ImoogDi/LesScope/doc/pictures/Backplane_bot_parts_mounted.png

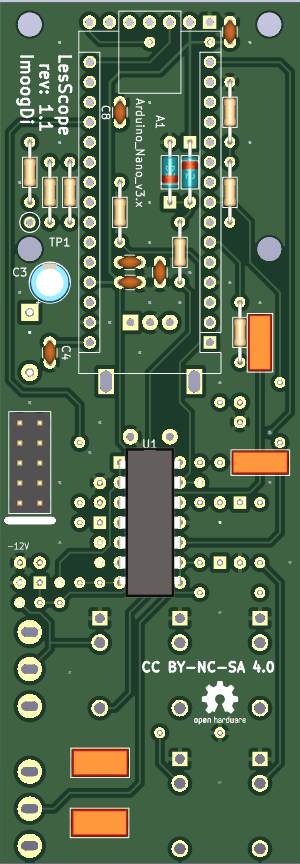
doc/pictures/Backplane_bot_parts_mounted.png
