ImoogDi/LesScope/doc/pictures/Backplane_top_parts_mounted.png

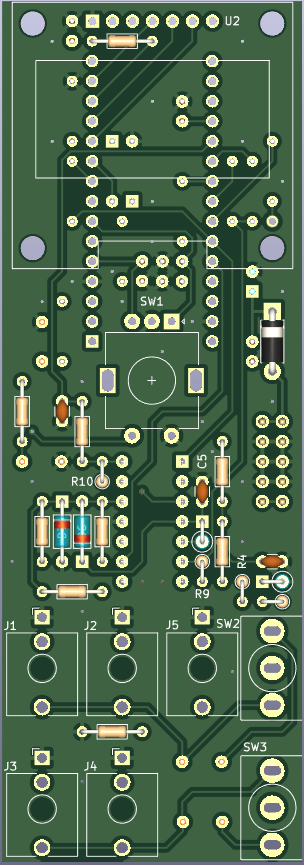
doc/pictures/Backplane_top_parts_mounted.png
